RyanMalawy/ECE-Capstone-Group-5/Spice/LTSpice/BinaryCounter.asc

Q1: npn
R1: res; 1k
R2: res; 5k
R3: res; 10k
R4: res; 10k
R5: res; 10k
R6: res; 20k
R7: res; 40k
R8: res; 60k
R9: res; 80k
R10: res; 100k
R11: res; 10k
R12: res; 10k
U1: DIP16; 74HC161
U2: DIP16; X
V1: voltage; PULSE(0 5 0 1n 1n 1u 10u)
V2: voltage; 5
V3: voltage; 5
V4: voltage; 4
V5: voltage; 3
Named nets: 0
.include 74hc.lib
.tran 0 1m 0 100n
.param vcc=5 speed=1 tripdt=0
.include dip.s
.include hc_tfast.cir
.include dhvqfn.s
