RyanMalawy/ECE-Capstone-Group-5/Spice/LTSpice/hc/hc_tnomi.cir

* HCMOS Subcircuit and Primitive Elements Library
* HC_TNOMI.CIR
* Nominal Process Corner
* Standard Logic Product Group
* NXP Semiconductors
*
* Version Date       By   Remarks
* ---------------------------------------------------------------------
*    1.3  01/02/2022 KDD  Added HC(T)10 & HC(T)11
*    1.2  30/03/2011 RRV  Rewritten netlists to add package options.
*    1.12 27/10/2010 RRV  Added HC(T)240/253
*    1.11 06/07/2010 RRV  Added HC(T)02/08/86
*    1.10 10/12/2009 RRV  Removed HCT05
*    1.09 09/22/2009 RRV  Corrected typo in SWITCH3N
*    1.08 09/08/2009 RRV  Added HC(T)4020/4060
*    1.07 03/27/2009 RRV  Added HC(T)05
*    1.06 02/20/2006 RRV  Added HC(T)366/368
*    1.05 10/27/2005 RRV  Updated HC/T04 and HCU04 models
*    1.04 09/22/2003 RM   Active High Enable for SWI2 and SWI2T
*
************************************************
*         NOMINAL N-Channel Transistor         *
*            UCB-3 Parameter Set               *
*         HIGH-SPEED CMOS Logic Family         *
*                10-Jan.-1995                  *
************************************************
.Model MHCNEN NMOS
+LEVEL = 3
+KP    = 45.3E-6
+VTO   = 0.72
+TOX   = 51.5E-9
+NSUB  = 2.8E15
+GAMMA = 0.94
+PHI   = 0.65
+VMAX  = 150E3
+RS    = 40
+RD    = 40
+XJ    = 0.11E-6
+LD    = 0.52E-6
+DELTA = 0.315
+THETA = 0.054
+ETA   = 0.025
+KAPPA = 0.0
+WD    = 0.0

***********************************************
*        NOMINAL P-Channel transistor         *
*           UCB-3 Parameter Set               *
*         HIGH-SPEED CMOS Logic Family        *
*               10-Jan.-1995                  *
***********************************************
.Model MHCPEN PMOS
+LEVEL = 3
+KP    = 22.1E-6
+VTO   = -0.71
+TOX   = 51.5E-9
+NSUB  = 3.3E16
+GAMMA = 0.92
+PHI   = 0.65
+VMAX  = 970E3
+RS    = 80
+RD    = 80
+XJ    = 0.63E-6
+LD    = 0.23E-6
+DELTA = 2.24
+THETA = 0.108
+ETA   = 0.322
+KAPPA = 0.0
+WD    = 0.0


.MODEL  INT D


****************************************
*   START OF SUB-CIRCUIT DESCRIPTION   *
*            MARCH 30, 2011            *
****************************************

*****NOMIN.CIR*****

****Version 1.04 Added Inverter****
.SUBCKT INV4N   2  3  50  60
*IN=2, OUT=3, VCC=50, GND=60
MP1 3  2 50 50  MHCPEN W=  88U L=2.4U AD= 350P AS= 350P PD=100U PS=  88U
MN1 3  2 60 60  MHCNEN W=  56U L=2.4U AD= 225P AS= 225P PD= 70U PS=  56U
.ENDS


.SUBCKT INP0N  2  3  50  60
*IN=2, OUT=3, VCC=50, GND=60
R1  2  3  100
MP1 3 50 50 50  MHCPEN W=20U L=2.4U AD=100P AS=100P PD=40U PS= 20U
MN1 3 60 60 60  MHCNEN W=35U L=2.4U AD=260P AS=260P PD=70U PS= 20U
.ENDS

.SUBCKT INP1N  2  3  50  60
*IN=2, OUT=3, VCC=50, GND=60
R1  2  4  100
MP1 4 50 50 50  MHCPEN W=20U L=2.4U AD=100P AS=100P PD=40U PS= 20U
MN1 4 60 60 60  MHCNEN W=35U L=2.4U AD=260P AS=260P PD=70U PS= 20U
MP2 3  4 50 50  MHCPEN W=88U L=2.4U AD=290P AS=550P PD=10U PS=100U
MN2 3  4 60 60  MHCNEN W=56U L=2.4U AD=162P AS=550P PD=10U PS= 75U
.ENDS

.SUBCKT INP1TN  2  3  50  60
*IN=2, OUT=3, VCC=50, GND=60
R1  2  4  100
MP1 4 50 50 50  MHCPEN W= 20U L=2.4U AD=100P AS=100P PD= 40U PS= 20U
MN1 4 60 60 60  MHCNEN W= 35U L=2.4U AD=260P AS=260P PD= 70U PS= 20U
MP2 3  4  5 50  MHCPEN W= 88U L=2.4U AD=290P AS=550P PD=107U PS=195U
MN2 3  4 60 60  MHCNEN W= 56U L=2.4U AD=162P AS=550P PD= 55U PS=162U
D1 50  5  INT
MP4 3  6 50 50  MHCPEN W=6.4U L=4.0U AD= 60P AS= 60P PD=13U PS= 24U
MN4 3  4 60 60  MHCNEN W=185U L=2.4U AD=740P AS=740P PD=50U PS=185U
MP5 6  3 50 50  MHCPEN W=6.4U L=3.2U AD= 50P AS= 50P PD=10U PS= 20U
MN5 6  3 60 60  MHCNEN W=6.4U L=3.2U AD= 50P AS= 50P PD=10U PS= 20U
.ENDS

.SUBCKT INP2N  2  3  50  60
*IN=2, OUT=3, VCC=50, GND=60
R1  2  4  100
MP1 4 50 50 50  MHCPEN W= 20U L=2.4U AD=100P AS=100P PD=40U PS= 20U
MN1 4 60 60 60  MHCNEN W= 35U L=2.4U AD=260P AS=260P PD=70U PS= 20U
MP2 3  4 50 50  MHCPEN W=176U L=2.4U AD=580P AS=580P PD=10U PS=200U
MN2 3  4 60 60  MHCNEN W=112U L=2.4U AD=325P AS=580P PD=10U PS=150U
.ENDS

.SUBCKT INP2TN  2  3  50  60
*IN=2, OUT=3, VCC=50, GND=60
R1  2  4  100
MP1 4 50 50 50  MHCPEN W= 20U L=2.4U AD=100P AS= 100P PD=40U PS= 20U
MN1 4 60 60 60  MHCNEN W= 35U L=2.4U AD=260P AS= 260P PD=70U PS= 20U
MP2 3  4  5 50  MHCPEN W=176U L=2.4U AD=580P AS=1100P PD=10U PS=200U
MN2 3  4 60 60  MHCNEN W=112U L=2.4U AD=325P AS=1100P PD=10U PS=150U
D1 50  5   INT
MP4 3  6 50 50  MHCPEN W=6.4U L=4.0U AD= 60P AS= 60P PD=13U PS= 24U
MN4 3  4 60 60  MHCNEN W=348U L=2.4U AD=740P AS=740P PD=50U PS=348U
MP5 6  3 50 50  MHCPEN W=6.4U L=3.2U AD= 50P AS= 50P PD=10U PS= 20U
MN5 6  3 60 60  MHCNEN W=6.4U L=3.2U AD= 50P AS= 50P PD=10U PS= 20U
.ENDS


.SUBCKT SMT1N  2  3  50  60
* SCHMITT-TRIGGER INPUT FOR HC14 CMOS INPUT LEVELS
*IN=2, OUT=3, VCC=50, GND=60
R1  2  4  100
MP1 4 50 50 50  MHCPEN W=20U L=2.4U AD=100P AS=100P PD=40U PS=20U
MN1 4 60 60 60  MHCNEN W=35U L=2.4U AD=140P AS=140P PD=50U PS=35U
MP2 5  4 50 50  MHCPEN W=36U L=2.4U AD=140P AS=140P PD=50U PS=35U
MN2 6  4 60 60  MHCNEN W=16U L=2.4U AD= 70P AS= 70P PD=15U PS=17U
MP3 3  4  5 50  MHCPEN W=44U L=2.4U AD=220P AS=220P PD=60U PS=44U
MN3 3  4  6  6  MHCNEN W=17U L=2.4U AD= 70P AS= 70P PD=15U PS=16U
MP4 5  3 60 50  MHCPEN W=36U L=2.4U AD=150P AS=150P PD=60U PS=36U
MN4 6  3 50  6  MHCNEN W= 6U L=  4U AD= 25P AS= 25P PD=10U PS= 6U
.ENDS


.SUBCKT SMTTL1N  2  3  50  60
* SCHMITT-TRIGGER INPUT FOR HCT14 WITH TTL INPUT LEVELS
*IN=2, OUT=3, VCC=50, GND=60
R1  2  4  100
MP1 4 50 50 50  MHCPEN W= 20U L=2.4U AD= 100P AS= 100P PD= 40U PS= 20U
MN1 4 60 60 60  MHCNEN W= 35U L=2.4U AD= 140P AS= 140P PD= 50U PS= 35U
D1  50  7  INT
MP2 5  4  7  7  MHCPEN W= 36U L=2.4U AD= 140P AS= 140P PD= 50U PS= 35U
MN2 6  4 60 60  MHCNEN W=216U L=2.4U AD= 860P AS= 860P PD=140U PS=216U
MP3 3  4  5 50  MHCPEN W= 54U L=2.4U AD= 220P AS= 220P PD= 60U PS= 44U
MN3 3  4  6  6  MHCNEN W=257U L=2.4U AD=1000P AS=1000P PD=150U PS=257U
MP4 5  3 60 50  MHCPEN W= 32U L=  4U AD= 120P AS= 120P PD=100U PS= 32U
MN4 6  3 50  6  MHCNEN W= 14U L=  4U AD= 100P AS= 100P PD= 30U PS= 24U
MP5 8  3 50 50  MHCPEN W= 10U L=2.4U AD=  40P AS=  40P PD= 16U PS= 10U
MN5 8  3 60 60  MHCNEN W=  5U L=2.4U AD=  20P AS=  20P PD= 12U PS=  5U
MP6 3  8 50 50  MHCPEN W=  6U L=8.0U AD=  30P AS=  30P PD= 16U PS=  6U
.ENDS


.SUBCKT INVN   2  3  50  60
*IN=2, OUT=3, VCC=50, GND=60
MP1 3  2 50 50  MHCPEN W=364U L=2.4U AD=500P  AS=500P PD=10U PS=430U
MN1 3  2 60 60  MHCNEN W=184U L=2.4U AD=275P  AS=275P PD=10U PS=270U
.ENDS


.SUBCKT NANDN  2  3  4  50  60
*INTERNAL NAND
*IN1 = 2, IN2 = 3, OUT = 4, VCC= 50, GND = 60
MP1 4  2  50  50  MHCPEN W=112U  L=2.4U AD=150P AS=300P PD= 75U PS=150U
MP2 4  3  50  50  MHCPEN W=112U  L=2.4U AD=150P AS=300P PD= 75U PS=150U
MN1 4  2   5  60  MHCNEN W=300U  L=2.4U AD=300P AS=300P PD=300U PS=300U
MN2 5  3  60  60  MHCNEN W=300U  L=2.4U AD=300P AS=300P PD=300U PS=300U
.ENDS

.SUBCKT LLCN  2  3  40  50  60
* LEVEL CONVERTER
* INA = 2,  OUT = 3,  VEE = 40,  VCC = 50,  GND =  60
MP4 4  2  50  50  MHCPEN W= 30U  L= 2.4U AD=120P AS=120P PD= 40U PS= 30U
MN4 4  2  60  60  MHCNEN W= 15U  L= 2.4U AD= 60P AS= 60P PD= 20U PS= 15U
MP1 5  4  50  50  MHCPEN W=135U  L= 2.4U AD=500P AS=500P PD=100U PS=135U
MP2 6  2  50  50  MHCPEN W=135U  L= 2.4U AD=500P AS=500P PD=100U PS=135U
MN1 5  6  40  40  MHCNEN W=6.4U  L=18.8U AD= 25P AS= 25P PD= 20U PS=6.4U
MN2 6  5  40  40  MHCNEN W=6.4U  L=18.8U AD= 25P AS= 25P PD= 20U PS=6.4U
MP3 7  6  50  50  MHCPEN W= 10U  L= 4.0U AD= 40P AS= 40P PD= 20U PS= 10U
MN3 7  6  40  40  MHCNEN W=  5U  L= 4.0U AD= 20P AS= 20P PD= 10U PS=  5U
MP5 3  7  50  50  MHCPEN W= 30U  L= 2.4U AD=120P AS=120P PD= 40U PS= 30U
MN5 3  7  40  40  MHCNEN W= 15U  L= 2.4U AD= 60P AS= 60P PD= 20U PS= 15U
.ENDS

.SUBCKT SWITCH1N  2  8  9  40  50
* ANALOG SWITCH
* INPUT = 2,   Y = 8,  Z = 9,  VEE = 40,  VCC =50
MP1 3  2  50  50  MHCPEN W=  88U L=2.4U AD= 350P AS= 350P PD=100U PS=  88U
MN1 3  2  40  40  MHCNEN W=  56U L=2.4U AD= 225P AS= 225P PD= 70U PS=  56U
MP4 4  3  50  50  MHCPEN W= 350U L=2.4U AD= 900P AS= 900P PD=200U PS= 350U
MN4 4  3  40  40  MHCNEN W= 150U L=2.4U AD= 400P AS= 400P PD=100U PS= 150U
MP5 8  4   5  50  MHCPEN W= 216U L=2.4U AD= 900P AS= 900P PD=100U PS= 216U
MN5 8  3   5   5  MHCNEN W= 108U L=2.4U AD= 430P AS= 430P PD= 50U PS= 108U
MN6 5  4  40  40  MHCNEN W= 145U L=2.4U AD= 600P AS= 600P PD= 75U PS= 145U
MP7 9  4   8  50  MHCPEN W=1068U L=2.4U AD=2500P AS=2500P PD= 10U PS=1068U
MN7 9  3   8   5  MHCNEN W= 312U L=2.4U AD=1200P AS=1200P PD= 10U PS= 312U
.ENDS

.SUBCKT SWITCH2N  2  8  9  50  60
* ANALOG SWITCH
* INPUT= 2   Y= 8   Z= 9  VCC= 50   GND= 60
MP1 3  2  50  50  MHCPEN W=  88U L=2.4U AD= 350P AS= 350P PD=100U PS=  88U
MN1 3  2  60  60  MHCNEN W=  56U L=2.4U AD= 225P AS= 225P PD= 70U PS=  56U
MP4 4  3  50  50  MHCPEN W= 350U L=2.4U AD= 900P AS= 900P PD=200U PS= 350U
MN4 4  3  60  60  MHCNEN W= 150U L=2.4U AD= 400P AS= 400P PD=100U PS= 150U
MP5 5  3   8  50  MHCPEN W=  85U L=2.4U AD= 355P AS= 355P PD= 40U PS=  85U
MN5 5  4   8   5  MHCNEN W=  42U L=2.4U AD= 170P AS= 170P PD= 20U PS=  42U
MN6 5  3  60  60  MHCNEN W= 145U L=2.4U AD= 600P AS= 600P PD= 75U PS= 145U
MP7 9  3   8  50  MHCPEN W=1900U L=2.4U AD=2500P AS=2500P PD= 10U PS=1900U
MN7 9  4   8   5  MHCNEN W= 576U L=2.4U AD=1200P AS=1200P PD= 10U PS= 576U
.ENDS

.SUBCKT SWITCH3N  2  8  9  40  50
* ANALOG SWITCH
* INPUT = 2   Y = 8  Z = 9  VEE = 40  VCC = 50
MP1 3  2  50  50  MHCPEN W=  88U L=2.4U AD= 350P AS= 350P PD=100U PS=  88U
MN1 3  2  40  40  MHCNEN W=  56U L=2.4U AD= 225P AS= 225P PD= 70U PS=  56U
MP4 4  3  50  50  MHCPEN W= 350U L=2.4U AD= 900P AS= 900P PD=200U PS= 350U
MN4 4  3  40  40  MHCNEN W= 150U L=2.4U AD= 400P AS= 400P PD=100U PS= 150U
MP5 9  3   8  50  MHCPEN W=1168U L=2.4U AD=2730P AS=2730P PD= 10U PS=1168U
MN5 9  4   8  40  MHCNEN W= 312U L=2.4U AD=1200P AS=1200P PD= 10U PS= 312U
.ENDS


.SUBCKT BUSOUTPN  2   3   4   50   60
* INPUT = 2  OEN = 3 (LOW)  OUT = 4  VCC = 50  GND = 60
* 3-STATE BUS OUTPUT
MP1 5  3   50  50  MHCPEN W= 90U  L=2.4U AD= 360P AS= 360P PD= 30U PS=360U
MN1 5  3   60  60  MHCNEN W= 40U  L=2.4U AD= 160P AS= 160P PD= 20U PS= 40U
MP2 6  2   50  50  MHCPEN W=480U  L=2.4U AD=1800P AS=1800P PD=100U PS=480U
MN2 7  2   60  60  MHCNEN W=240U  L=2.4U AD=1000P AS=1000P PD= 50U PS=240U
MP3 7  3    6  50  MHCPEN W=280U  L=2.4U AD=1120P AS=1120P PD= 55U PS=280U
MN3 7  3   60  60  MHCNEN W=160U  L=2.4U AD= 640P AS= 640P PD= 40U PS=160U
MP4 6  5   50  50  MHCPEN W=240U  L=2.4U AD=1000P AS=1000P PD= 50U PS=240U
MN4 7  5    7  60  MHCNEN W=190U  L=2.4U AD= 760P AS= 760P PD= 45U PS=190U
R1  6  8  200
R2  7  9  200
MP5 4  8   50  50  MHCPEN W=540U  L=2.4U AD=1500P AS=1500P PD=10U PS=540U
MN5 4  9   60  60  MHCNEN W=233U  L=2.4U AD= 750P AS= 750P PD=10U PS=233U
R3  8  10 100
R4  9  11 100
MP6 4  10  50  50  MHCPEN W=540U  L=2.4U AD=1500P AS=1500P PD=10U PS=540U
MN6 4  11  60  60  MHCNEN W=233U  L=2.4U AD= 750P AS= 750P PD=10U PS=233U
R5 10  12  50
R6 11  13  50
MP7 4  12  50  50  MHCPEN W=540U  L=2.4U AD=1500P AS=1500P PD=10U PS=540U
MN7 4  13  60  60  MHCNEN W=233U  L=2.4U AD= 750P AS= 750P PD=10U PS=233U
.ENDS

.SUBCKT OUTUN 2  3  50  60
*IN=2, OUT=3, VCC=50, GND=60
R1  2 4 100
MP1 3 4 50 50  MHCPEN W=485U L=2.4U AD=1200P AS=530P PD=10U PS=180U
MN1 3 4 60 60  MHCNEN W=222U L=2.4U AD=530P AS=300P PD=10U PS=130U
R2  4 5 50
MP2 3 5 50 50  MHCPEN W=485U L=2.4U AD=1200P AS=530P PD=10U PS=180U
MN2 3 5 60 60  MHCNEN W=222U L=2.4U AD=530P AS=300P PD=10U PS=130U
R3  5 6 50
MP3 3 6 50 50  MHCPEN W=485U L=2.4U AD=1200P AS=530P PD=10U PS=180U
MN3 3 6 60 60  MHCNEN W=222U L=2.4U AD=530P AS=300P PD=10U PS=130U
.ENDS

.SUBCKT OUTPN 2  3  50  60
*IN=2, OUT=3, VCC=50, GND=60
R1  2 4 100
MP1 3 4 50 50  MHCPEN W=360U L=2.4U AD=400P AS=400P PD=10U PS=180U
MN1 3 4 60 60  MHCNEN W=140U L=2.4U AD=200P AS=300P PD=10U PS=130U
R2  4 5 50
MP2 3 5 50 50  MHCPEN W=360U L=2.4U AD=400P AS=400P PD=10U PS=180U
MN2 3 5 60 60  MHCNEN W=140U L=2.4U AD=200P AS=200P PD=10U PS=130U
R3  5 6 50
MP3 3 6 50 50  MHCPEN W=360U L=2.4U AD=400P AS=400P PD=10U PS=180U
MN3 3 6 60 60  MHCNEN W=140U L=2.4U AD=200P AS=200P PD=10U PS=130U
.ENDS

.SUBCKT OUTPODN 2  3  60
*IN=2, OUT=3, GND=60
R1  2 4 50
MN1 3 4 60 60  MHCNEN W=140U L=2.4U AD=200P AS=300P PD=10U PS=130U
R2  4 5 25
MN2 3 5 60 60  MHCNEN W=140U L=2.4U AD=200P AS=200P PD=10U PS=130U
R3  5 6 25
MN3 3 6 60 60  MHCNEN W=140U L=2.4U AD=200P AS=200P PD=10U PS=130U
.ENDS

.SUBCKT INPOSCN  2  5  3  50  60
R1  2  4  100
MP1 4 50 50 50  MHCPEN W=20U  L=2.4U AD=100P AS=100P PD=40U PS=20U
MN1 4 60 60 60  MHCNEN W=35U  L=2.4U AD=260P AS=260P PD=70U PS=20U
MP2 6  4 50 50  MHCPEN W=707U L=2.4U AD=1700P AS=2000P PD=40U PS=60U
MP3 6  5 50 50  MHCPEN W=166U L=2.4U AD=400P AS=800P PD=40U PS=60U
MN2 6  4  7 60  MHCNEN W=480U L=2.4U AD=1200P AS=900P PD=60U PS=65U
MN3 7  5 60 60  MHCNEN W=640U L=2.4U AD=1200P AS=2000P PD=90U PS=80U
MP4 3  6 50 50  MHCPEN W=832U L=2.4U AD=2000P AS=3000P PD=40U PS=60U
MN4 3  6 60 60  MHCNEN W=333U L=2.4U AD=800P AS=1600P PD=40U PS=60U
.ENDS

.SUBCKT INP3N  2  3  50  60
*IN=2, OUT=3, VCC=50, GND=60
R1  2  4  100
MP1 4 50 50 50  MHCPEN W=20U  L=2.4U AD=100P AS=100P PD=40U PS=20U
MN1 4 60 60 60  MHCNEN W=35U  L=2.4U AD=260P AS=260P PD=70U PS=20U
MP2 5  4 50 50  MHCPEN W=29U  L=2.4U AD=85P AS=85P PD=29U PS=29U
MN2 5  4 60 60  MHCNEN W=19U  L=2.4U AD=70P AS=70P PD=19U PS=19U
MP3 3  5 50 50  MHCPEN W=112U L=2.4U AD=200P AS=200P PD=30U PS=30U
MN3 3  5 60 60  MHCNEN W=56U  L=2.4U AD=100P AS=100P PD=15U PS=15U
.ENDS

.SUBCKT INP3TN  2  3  50  60
*IN=2, OUT=3, VCC=50, GND=60
R1  2  4  100
MP1 4 50 50 50  MHCPEN W=20U  L=2.4U AD=100P AS=100P PD=40U PS=20U
MN1 4 60 60 60  MHCNEN W=35U  L=2.4U AD=260P AS=260P PD=70U PS=20U
MP2 6  4  5 50  MHCPEN W=29U  L=2.4U AD=85P AS=85P PD=29U PS=29U
MN2 6  4 60 60  MHCNEN W=19U  L=2.4U AD=70P AS=70P PD=19U PS=19U
D1 50  5   INT
MP4 6  3 50 50  MHCPEN W=6.4U L=4.0U AD=25P AS=25P PD=6.4U PS=6.4U
MN4 6  4 60 60  MHCNEN W=80U  L=2.4U AD=120P AS=240P PD=80U PS=80U
MP5 3  6 50 50  MHCPEN W=112U L=3.2U AD=200P AS=200P PD=30U PS=30U
MN5 3  6 60 60  MHCNEN W=56U  L=3.2U AD=100P AS=100P PD=15U PS=15U
.ENDS
*******************************************************************
*******************************************************************

******CIR_NOMIN-HC TYPES******

.SUBCKT INV0  20 30 80 90
*IN=20, OUT=30, VCC=80, GND=90
XINP  20  25  80  90    INP0N
XOUTP 25  30  80  90    OUTUN
.ENDS


.SUBCKT INV1  20 30 80 90
*IN=20, OUT=30, VCC=80, GND=90
XINP  20  25  80  90    INP1N
XINV  25  35  80  90    INVN
XOUTP 35  30  80  90    OUTPN
.ENDS


.SUBCKT INV2  20  30  80 90
*IN=20, OUT=30, VCC=80, GND=90
XINP  20  25  80  90    INP2N
XINV  25  35  80  90    INVN
XOUTP 35  30  80  90    OUTPN
.ENDS

.SUBCKT INVOD  20  30  80  90
*IN=20, OUT=30, VCC=80, GND=90
XINP    20  25  80  90    INP2N
XINV    25  35  80  90    INVN
XOUTPOD 35  30  90        OUTPODN
.ENDS

.SUBCKT INVSMT  20  30  80 90
*IN=20, OUT=30, VCC=80, GND=90
XINP  20  25  80  90    SMT1N
XINV  25  35  80  90    INVN
XOUTP 35  30  80  90    OUTPN
.ENDS

.SUBCKT NINV1  20  30  80 90
*IN=20, OUT=30, VCC=80, GND=90
XINP  20  25  80  90    INP1N
XINV0 25  35  80  90    INVN
XINV1 35  45  80  90    INVN
XOUTP 45  30  80  90    OUTPN
.ENDS

.SUBCKT NANDINV 20  50  30  80  90
*INVERTING 2-NAND
*EN = 50, IN = 20, OUT = 30, VCC = 80, GND = 90
XIN1  20  25      80  90   INP2N
XIN2  50  35      80  90   INP2N
XNAND 25  35  36  80  90   NANDN
XOUT  36  30      80  90   OUTPN
.ENDS

.SUBCKT SWI1  20  30  40  70  80  90
* INP = 20  Y = 30  Z = 40  VEE = 70  VCC = 80  GND = 90
XINP 20  25  80  90      INP2N
XLC  25  35  70  80  90  LLCN
XAS  35  30  40  70  80  SWITCH1N
.ENDS


.SUBCKT SWI2  20 30 40 80 90
* INP = 20 Y = 30 Z = 40 VCC = 80  GND = 90
*XINP  20  25  80  90      INP2N
****Version 1.04 Inserted inverter****
XINP  20  250      80  90  INP2N
XINV  250  25      80  90  INV4N
XAS   25   30  40  80  90  SWITCH2N
.ENDS


.SUBCKT SWI3  20  30  40  70  80  90
* INP = 20  Y = 30  Z = 40  VEE = 70  VCC = 80  GND = 90
XINP 20  25  80  90      INP1N
XLC  25  35  70  80  90  LLCN
XAS  35  30  40  70  80  SWITCH3N
.ENDS


.SUBCKT NINV3  20  50  30  80  90
* INP = 20  OEN = 50(LOW)  OUT = 30   VCC = 80  GND = 90
XINP      20  25  80  90      INP2N
XINV      25  35  80  90      INVN
XBUSOUTP  35  50  30  80  90  BUSOUTPN
.ENDS

.SUBCKT INV3  20  50  30  80  90
* INP = 20  OEN = 50(LOW)  OUT = 30   VCC = 80  GND = 90
XINP      20  25  80  90      INP2N
XBUSOUTP  25  50  30  80  90  BUSOUTPN
.ENDS

.SUBCKT OSC  20  50  30  80  90
*
* INP = 20  MR = 50  OUT = 30  VCC = 80  GND = 90
XINPOSC   20  17  25  80  90  INPOSCN
XINV1     25  35  80  90      INVN
XOUTPN    35  30  80  90      OUTPN
XINPMR	  50  16  80  90      INP3N
XINV2     16  17  80  90      INVN
.ENDS

******CIR_NOMIN-HCT TYPES******

.SUBCKT INV1T  20 30 80 90
*IN=20, OUT=30, VCC=80, GND=90
XINP  20  25  80  90    INP1TN
XINV  25  35  80  90    INVN
XOUTP 35  30  80  90    OUTPN
.ENDS


.SUBCKT INV2T  20  30  80 90
*IN=20, OUT=30, VCC=80, GND=90
XINP  20  25  80  90    INP2TN
XINV  25  35  80  90    INVN
XOUTP 35  30  80  90    OUTPN
.ENDS

.SUBCKT INVODT  20  30  80  90
*IN=20, OUT=30, VCC=80, GND=90
XINP    20  25  80  90    INP2TN
XINV    25  35  80  90    INVN
XOUTPOD 35  30  90        OUTPODN
.ENDS

.SUBCKT INVSMTT  20  30  80 90
*IN=20, OUT=30, VCC=80, GND=90
XINP  20  25  80  90    SMTTL1N
XINV  25  35  80  90    INVN
XOUTP 35  30  80  90    OUTPN
.ENDS

.SUBCKT NINV1T  20  30  80 90
*IN=20, OUT=30, VCC=80, GND=90
XINP  20  25  80  90    INP1TN
XINV0 25  35  80  90    INVN
XINV1 35  45  80  90    INVN
XOUTP 45  30  80  90    OUTPN
.ENDS

.SUBCKT NANDINVT 20  50  30  80  90
*INVERTING 2-NAND
*EN = 50, IN = 20, OUT = 30, VCC = 80, GND = 90
XIN1  20  25      80  90   INP2TN
XIN2  50  35      80  90   INP2TN
XNAND 25  35  36  80  90   NANDN
XOUT  36  30      80  90   OUTPN
.ENDS

.SUBCKT SWI1T  20  30  40  70  80  90
* INP = 20  Y = 30  Z = 40  VEE = 70  VCC = 80  GND = 90
XINP 20  25  80  90      INP2TN
XLC  25  35  70  80  90  LLCN
XAS  35  30  40  70  80  SWITCH1N
.ENDS


.SUBCKT SWI2T  20 30 40 80 90
* INP = 20 Y = 30 Z = 40 VCC = 80  GND = 90
*XINP  20  25  80  90      INP2TN
****Version 1.04 Inserted inverter****
XINP  20  250      80  90  INP2TN
XINV  250  25      80  90  INV4N
XAS   25   30  40  80  90  SWITCH2N
.ENDS


.SUBCKT SWI3T  20  30  40  70  80  90
* INP = 20  Y = 30  Z = 40  VEE = 70  VCC = 80  GND = 90
XINP 20  25  80  90      INP1TN
XLC  25  35  70  80  90  LLCN
XAS  35  30  40  70  80  SWITCH3N
.ENDS


.SUBCKT NINV3T  20  50  30  80  90
* INP = 20  OEN = 50(LOW)  OUT = 30   VCC = 80  GND = 90
XINP      20  25  80  90      INP2TN
XINV      25  35  80  90      INVN
XBUSOUTP  35  50  30  80  90  BUSOUTPN
.ENDS

.SUBCKT INV3T  20  50  30  80  90
* INP = 20  OEN = 50(LOW)  OUT = 30   VCC = 80  GND = 90
XINP      20  25  80  90      INP2TN
XBUSOUTP  25  50  30  80  90  BUSOUTPN
.ENDS

.SUBCKT OSCT  20  50  30  80  90
*
* INP = 20  MR = 50  OUT = 30  VCC = 80  GND = 90
XINPOSC   20  17  25  80  90  INPOSCN
XINV1     25  35  80  90      INVN
XOUTPN    35  30  80  90      OUTPN
XINPMR	  50  16  80  90      INP3TN
XINV2     16  17  80  90      INVN
.ENDS

***********************************************************
.SUBCKT HC00pck 2 3 1 0
*IN=2, OUT=3, VCC=1, GND=0
XHC00     20  30  10  90          INV2
XPK14  2 90  3 90 90 90  0 90 90 90 90 90 90  1 
+     20 90 30 90 90 90 90 90 90 90 90 90 90 10 pk14
.ENDS

.SUBCKT HCT00pck 2 3 1 0
*IN=2, OUT=3, VCC=1, GND=0
XHCT00    20  30  10  90          INV2T
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
+     90 90 90 90 90 90 90 90 90 90 90 90 50 20 30 10 pk16
.ENDS

.SUBCKT HCT595pck 2 5 3 1 0
XHCT595   20  50  30  10  90      NINV3T
XPK16 90 90 90 90 90 90 90  0 90 90 90 90  5  2  3  1 
+     90 90 90 90 90 90 90 90 90 90 90 90 50 20 30 10 pk16
.ENDS

.SUBCKT HC4020pck 2 3 1 0
XHC4020   20  30  10  90          NINV1
XPK16 90 90 90 90 90 90 90  0  3  2 90 90 90 90 90  1 
+     90 90 90 90 90 90 90 90 30 20 90 90 90 90 90 10 pk16
.ENDS

.SUBCKT HCT4020pck 2 3 1 0
XHCT4020  20  30  10  90          NINV1T
XPK16 90 90 90 90 90 90 90  0  3  2 90 90 90 90 90  1 
+     90 90 90 90 90 90 90 90 30 20 90 90 90 90 90 10 pk16
.ENDS
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
